vvvlc/RFM2Pi/hardware/RFM12Pi_V2.6/RFM12Pi_V1.6_sch.png

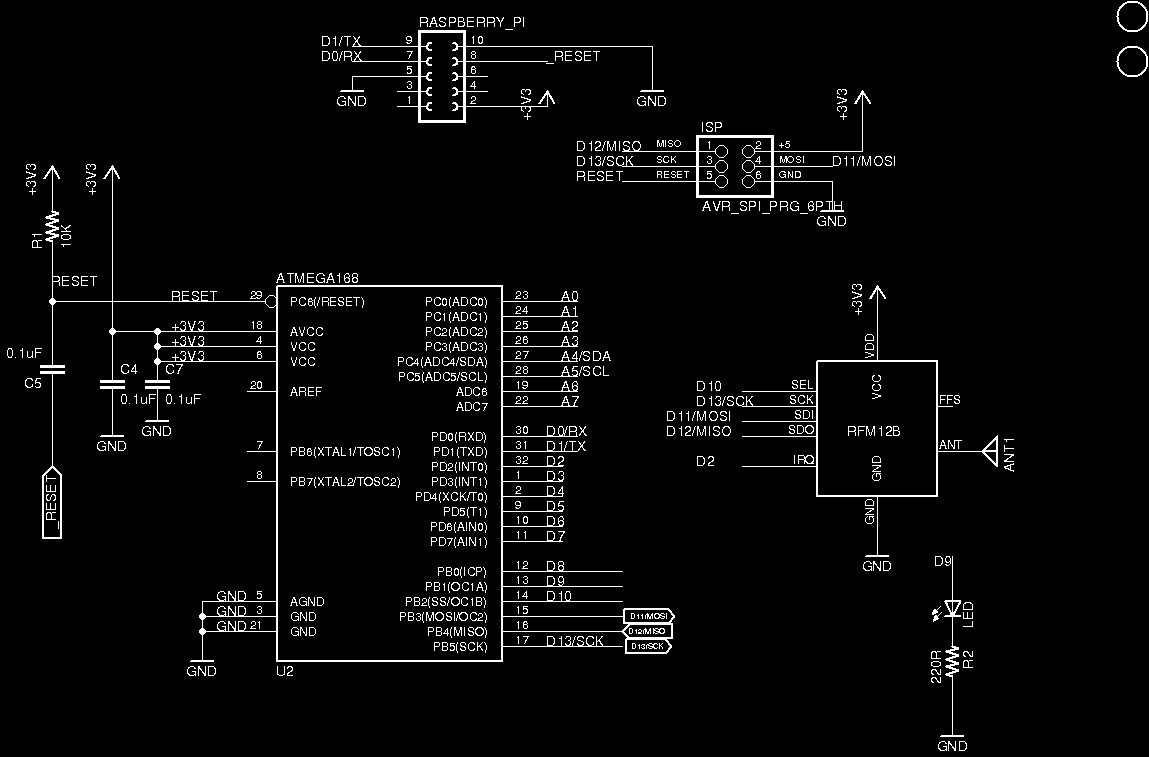
hardware/RFM12Pi_V2.6/RFM12Pi_V1.6_sch.png
