vvvlc/RFM2Pi/hardware/RFM69Pi_V3.1/RFM12Pi_V3.1_ISP_program.jpg

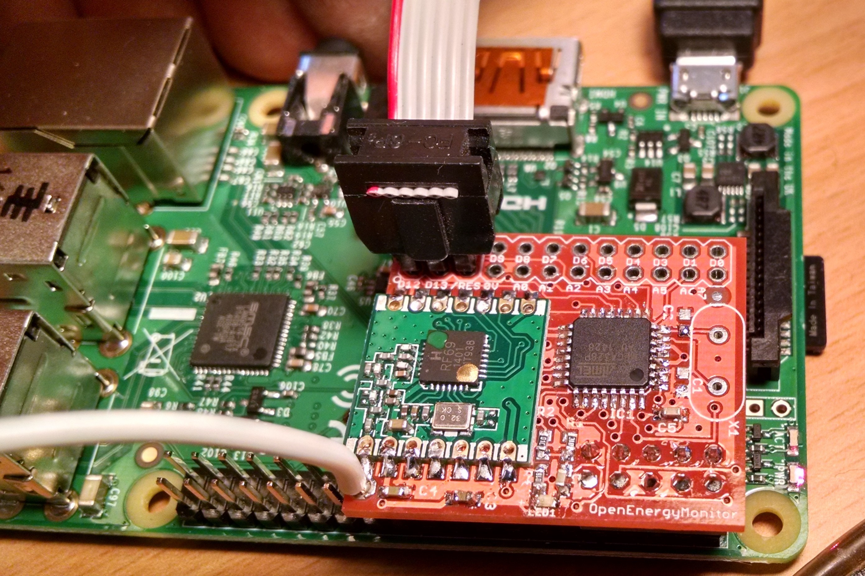
hardware/RFM69Pi_V3.1/RFM12Pi_V3.1_ISP_program.jpg
